rikulehtonen/einkframe/documentation/waveshare_documentation_4inch/4inch e-Paper HAT+ (E) Manual - Waveshare Wiki_files/300px-4inch_e-Paper_HAT+_(E).jpg

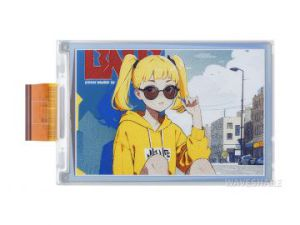
documentation/waveshare_documentation_4inch/4inch e-Paper HAT+ (E) Manual - Waveshare Wiki_files/300px-4inch_e-Paper_HAT+_(E).jpg
