rikulehtonen/einkframe/documentation/waveshare_documentation_4inch/4inch e-Paper HAT+ (E) Manual - Waveshare Wiki_files/E-paper_arduino_cede-R4-3.jpg

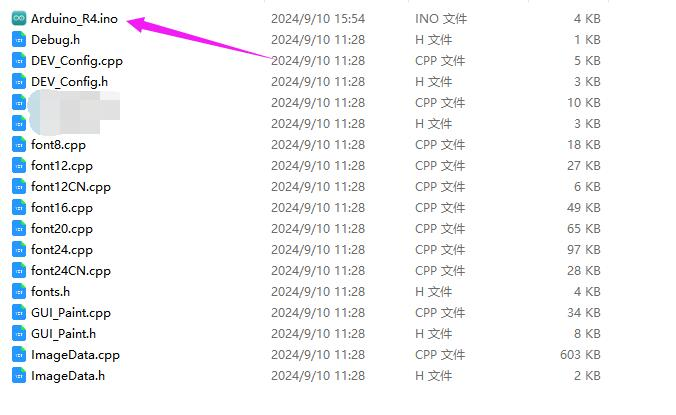
documentation/waveshare_documentation_4inch/4inch e-Paper HAT+ (E) Manual - Waveshare Wiki_files/E-paper_arduino_cede-R4-3.jpg
