rikulehtonen/einkframe/documentation/waveshare_documentation_4inch/4inch e-Paper HAT+ (E) Manual - Waveshare Wiki_files/E-paper_stm32_cede1_f103zet6.jpg

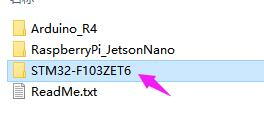
documentation/waveshare_documentation_4inch/4inch e-Paper HAT+ (E) Manual - Waveshare Wiki_files/E-paper_stm32_cede1_f103zet6.jpg
