rikulehtonen/einkframe/documentation/waveshare_documentation_4inch/4inch e-Paper HAT+ (E) Manual - Waveshare Wiki_files/STM32_for_4.37_e-paper012.jpg

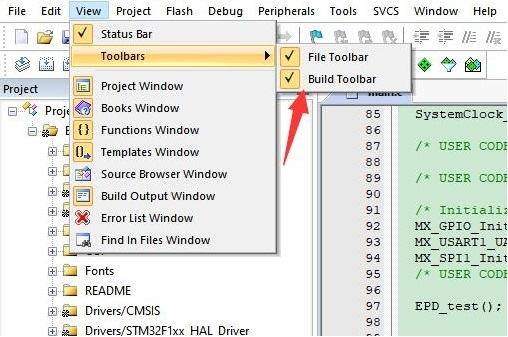
documentation/waveshare_documentation_4inch/4inch e-Paper HAT+ (E) Manual - Waveshare Wiki_files/STM32_for_4.37_e-paper012.jpg
