rikulehtonen/einkframe/documentation/waveshare_documentation_13inch/13.3inch e-Paper HAT+ (E) Manual - Waveshare Wiki_files/12.48-epaper-SPI-1.jpg

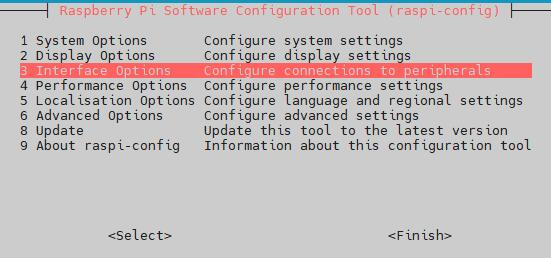
documentation/waveshare_documentation_13inch/13.3inch e-Paper HAT+ (E) Manual - Waveshare Wiki_files/12.48-epaper-SPI-1.jpg
