rikulehtonen/einkframe/documentation/waveshare_documentation_13inch/13.3inch e-Paper HAT+ (E) Manual - Waveshare Wiki_files/13.3inch-e-Paper-E-IC.jpg

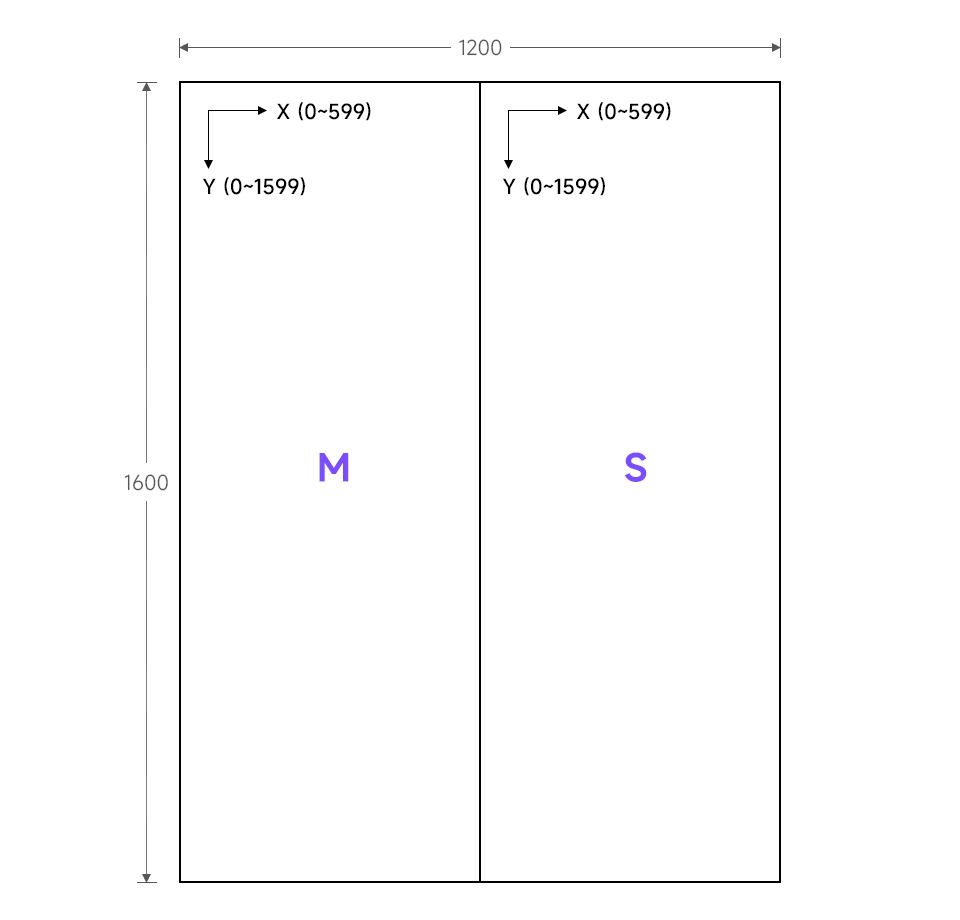
documentation/waveshare_documentation_13inch/13.3inch e-Paper HAT+ (E) Manual - Waveshare Wiki_files/13.3inch-e-Paper-E-IC.jpg
