rikulehtonen/einkframe/einkframe_communication.png

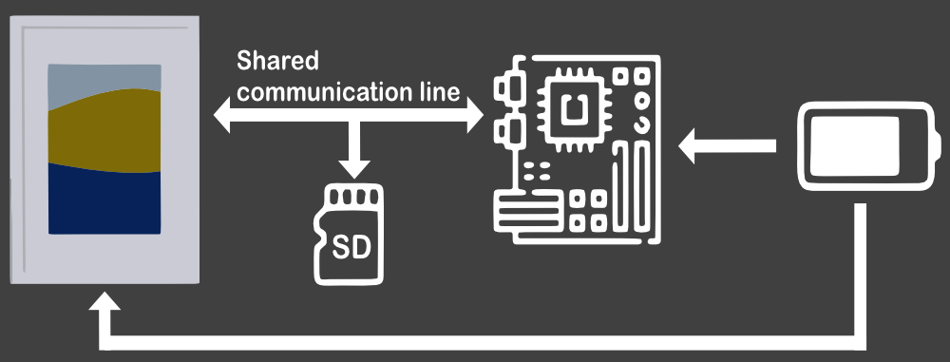
einkframe_communication.png
