rikulehtonen/einkframe/demo/waweshare-RaspberryPi_JetsonNano_4inch/python/pic/test.bmp

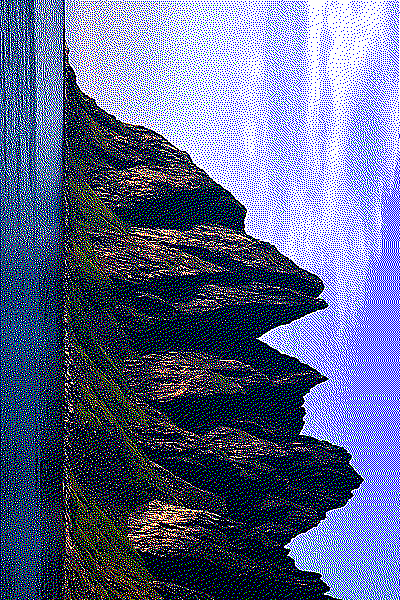
demo/waweshare-RaspberryPi_JetsonNano_4inch/python/pic/test.bmp
